ruckusmattster/xtm-led-driver/hardware/board_b/board_b-sheets.md

# Board B (controller): sheet tables

Generated by `design/build.py` from `design/board_b.py`. Every pin of every part is listed; `NC` means deliberately unconnected. Net names in CAPS match the KiCad netlist.

## Sheet B1: Power

| Ref | Value | Part | Footprint | Pins (pin name: net) |
| --- | --- | --- | --- | --- |
| C1 | 10uF | CL21A106KAYNNNE | `Capacitor_SMD:C_0805_2012Metric` | 1: +5V_SYS; 2: GND |
| D1 | B5819W | B5819W SL | `Diode_SMD:D_SOD-123` | 1 K: +5V_SYS; 2 A: +5V5_F |
| FB1 | 600R@100MHz 2A | UPZ2012E601-2R0TF | `Inductor_SMD:L_0805_2012Metric` | 1: +5V5_IN; 2: +5V5_F |
| J1 | 2x5 box header |  | `Connector_IDC:IDC-Header_2x05_P2.54mm_Vertical` | 1: +5V5_IN; 2: GND; 3: +5V5_IN; 4: GND; 5: TXD_A; 6: GND; 7: RXD_A; 8: BOOT0_A; 9: A_OK; 10: NRST_A |

Notes:

- **J1**: Same pinout as Board A's J3; a straight-through ribbon
- **D1**: Keeps the module's USB 5 V (its 5V pin) out of Board A when it's powered from USB
- **C1**: At U1's 5V pin

## Sheet B2: ESP32-S3-Zero

| Ref | Value | Part | Footprint | Pins (pin name: net) |
| --- | --- | --- | --- | --- |
| C3 | 100nF | CC0603KRX7R9BB104 | `Capacitor_SMD:C_0603_1608Metric` | 1: +3V3; 2: GND |
| U1 | ESP32-S3-Zero-M | ESP32-S3-Zero-M | `XTM:ESP32-S3-Zero_Socket` | 1 5V: +5V_SYS; 2 GND: GND; 3 3V3: +3V3; 4 GP1: LINK_TX; 5 GP2: LINK_RX; 6 GP3: SPARE_IO3; 7 GP4: ENC_A; 8 GP5: ENC_B; 9 GP6: ENC_SW; 10 GP7: SYNC; 11 GP8: BOOT0_OUT; 12 GP9: A_OK_IN; 13 GP10: NRST_OUT; 14 GP11: LED_R; 15 GP12: LED_G; 16 GP13: LED_B; 17 RX/GP44: SPARE_IO44; 18 TX/GP43: SPARE_IO43 |

Notes:

- **U1**: Plugged into two 1x9 sockets on the bottom side, component side away from the board, antenna end at the board edge. IO4-IO13 keep the WROOM design's assignments; the link moves to IO1/IO2 so UART0 (IO43/IO44, which the boot ROM talks on) stays off Board A's line. IO3 is a strapping pin: left as a spare
- **C3**: At U1's 3V3 pin

## Sheet B3: Controls, indicators and link

| Ref | Value | Part | Footprint | Pins (pin name: net) |
| --- | --- | --- | --- | --- |
| C8 | 10nF |  | `Capacitor_SMD:C_0603_1608Metric` | 1: ENC_A; 2: GND |
| C9 | 10nF |  | `Capacitor_SMD:C_0603_1608Metric` | 1: ENC_B; 2: GND |
| C10 | 10nF |  | `Capacitor_SMD:C_0603_1608Metric` | 1: ENC_SW; 2: GND |
| C11 | 10nF |  | `Capacitor_SMD:C_0603_1608Metric` | 1: SYNC; 2: GND |
| D3 | red | KT-0603R | `LED_SMD:LED_0603_1608Metric` | 1 K: LED_R; 2 A: LED_R_A |
| D4 | green | KT-0603G | `LED_SMD:LED_0603_1608Metric` | 1 K: LED_G; 2 A: LED_G_A |
| D5 | blue | KT-0603B | `LED_SMD:LED_0603_1608Metric` | 1 K: LED_B; 2 A: LED_B_A |
| FID1 | FID |  | `Fiducial:Fiducial_1mm_Mask2mm` |  |
| FID2 | FID |  | `Fiducial:Fiducial_1mm_Mask2mm` |  |
| FID3 | FID |  | `Fiducial:Fiducial_1mm_Mask2mm` |  |
| H1 | M3 |  | `MountingHole:MountingHole_3.2mm_M3` |  |
| H2 | M3 |  | `MountingHole:MountingHole_3.2mm_M3` |  |
| J3 | JST PH 2 | B2B-PH-K-S(LF)(SN) | `Connector_JST:JST_PH_B2B-PH-K_1x02_P2.00mm_Vertical` | 1: SYNC_RAW; 2: GND |
| J4 | 1x5 header |  | `Connector_PinHeader_2.54mm:PinHeader_1x05_P2.54mm_Vertical` | 1: +3V3; 2: SPARE_IO3; 3: SPARE_IO43; 4: SPARE_IO44; 5: GND |
| R7 | 10k | 0603WAF1002T5E | `Resistor_SMD:R_0603_1608Metric` | 1: +3V3; 2: ENC_A_RAW |
| R8 | 10k | 0603WAF1002T5E | `Resistor_SMD:R_0603_1608Metric` | 1: ENC_A_RAW; 2: ENC_A |
| R9 | 10k | 0603WAF1002T5E | `Resistor_SMD:R_0603_1608Metric` | 1: +3V3; 2: ENC_B_RAW |
| R10 | 10k | 0603WAF1002T5E | `Resistor_SMD:R_0603_1608Metric` | 1: ENC_B_RAW; 2: ENC_B |
| R11 | 10k | 0603WAF1002T5E | `Resistor_SMD:R_0603_1608Metric` | 1: +3V3; 2: ENC_SW_RAW |
| R12 | 10k | 0603WAF1002T5E | `Resistor_SMD:R_0603_1608Metric` | 1: ENC_SW_RAW; 2: ENC_SW |
| R13 | 10k | 0603WAF1002T5E | `Resistor_SMD:R_0603_1608Metric` | 1: +3V3; 2: SYNC_RAW |
| R14 | 10k | 0603WAF1002T5E | `Resistor_SMD:R_0603_1608Metric` | 1: SYNC_RAW; 2: SYNC |
| R15 | 1k | 0603WAF1001T5E | `Resistor_SMD:R_0603_1608Metric` | 1: +3V3; 2: LED_R_A |
| R16 | 220R | 0603WAF2200T5E | `Resistor_SMD:R_0603_1608Metric` | 1: +3V3; 2: LED_G_A |
| R17 | 220R | 0603WAF2200T5E | `Resistor_SMD:R_0603_1608Metric` | 1: +3V3; 2: LED_B_A |
| R18 | 100R | 0603WAF1000T5E | `Resistor_SMD:R_0603_1608Metric` | 1: LINK_TX; 2: RXD_A |
| R19 | 100R | 0603WAF1000T5E | `Resistor_SMD:R_0603_1608Metric` | 1: TXD_A; 2: LINK_RX |
| R20 | 100R | 0603WAF1000T5E | `Resistor_SMD:R_0603_1608Metric` | 1: BOOT0_OUT; 2: BOOT0_A |
| R21 | 100R | 0603WAF1000T5E | `Resistor_SMD:R_0603_1608Metric` | 1: A_OK; 2: A_OK_IN |
| R22 | 100k | 0603WAF1003T5E | `Resistor_SMD:R_0603_1608Metric` | 1: A_OK_IN; 2: GND |
| R23 | 100R | 0603WAF1000T5E | `Resistor_SMD:R_0603_1608Metric` | 1: NRST_OUT; 2: NRST_A |
| SW3 | PEC11R-4220F-S0024 | PEC11R-4220F-S0024 | `Rotary_Encoder:RotaryEncoder_Alps_EC11E-Switch_Vertical_H20mm_CircularMountingHoles` | A A: ENC_A_RAW; B B: ENC_B_RAW; C C: GND; S1 S1: ENC_SW_RAW; S2 S2: GND; MP MP: GND |
| SW4 | SYNC |  | `Button_Switch_SMD:SW_SPST_B3S-1000` | 1: SYNC_RAW; 2: GND |
| TP1 | TP |  | `TestPoint:TestPoint_Pad_D1.0mm` | 1: +5V_SYS |
| TP2 | TP |  | `TestPoint:TestPoint_Pad_D1.0mm` | 1: +3V3 |
| TP3 | TP |  | `TestPoint:TestPoint_Pad_D1.0mm` | 1: GND |

Notes:

- **SW3**: Mounting lugs to GND
- **J3**: External panel sync button in parallel with SW4
- **R22**: Unplugged ribbon reads as 'Board A not OK'
- **R23**: IO10 is driven open-drain by firmware
- **J4**: Optional spare header: IO43/IO44 are UART0 (the ESP32's console), IO3 a strapping pin

## Net list

| Net | Connections |
| --- | --- |
| +3V3 | C3.1, J4.1, R7.1, R9.1, R11.1, R13.1, R15.1, R16.1, R17.1, TP2.1, U1.3 |
| +5V5_F | D1.2, FB1.2 |
| +5V5_IN | FB1.1, J1.1, J1.3 |
| +5V_SYS | C1.1, D1.1, TP1.1, U1.1 |
| A_OK | J1.9, R21.1 |
| A_OK_IN | R21.2, R22.1, U1.12 |
| BOOT0_A | J1.8, R20.2 |
| BOOT0_OUT | R20.1, U1.11 |
| ENC_A | C8.1, R8.2, U1.7 |
| ENC_A_RAW | R7.2, R8.1, SW3.A |
| ENC_B | C9.1, R10.2, U1.8 |
| ENC_B_RAW | R9.2, R10.1, SW3.B |
| ENC_SW | C10.1, R12.2, U1.9 |
| ENC_SW_RAW | R11.2, R12.1, SW3.S1 |
| GND | C1.2, C3.2, C8.2, C9.2, C10.2, C11.2, J1.2, J1.4, J1.6, J3.2, J4.5, R22.2, SW3.C, SW3.MP, SW3.S2, SW4.2, TP3.1, U1.2 |
| LED_B | D5.1, U1.16 |
| LED_B_A | D5.2, R17.2 |
| LED_G | D4.1, U1.15 |
| LED_G_A | D4.2, R16.2 |
| LED_R | D3.1, U1.14 |
| LED_R_A | D3.2, R15.2 |
| LINK_RX | R19.2, U1.5 |
| LINK_TX | R18.1, U1.4 |
| NRST_A | J1.10, R23.2 |
| NRST_OUT | R23.1, U1.13 |
| RXD_A | J1.7, R18.2 |
| SPARE_IO3 | J4.2, U1.6 |
| SPARE_IO43 | J4.3, U1.18 |
| SPARE_IO44 | J4.4, U1.17 |
| SYNC | C11.1, R14.2, U1.10 |
| SYNC_RAW | J3.1, R13.2, R14.1, SW4.1 |
| TXD_A | J1.5, R19.1 |
