ruckusmattster/xtm-led-driver/docs/images/board-a-iso.png

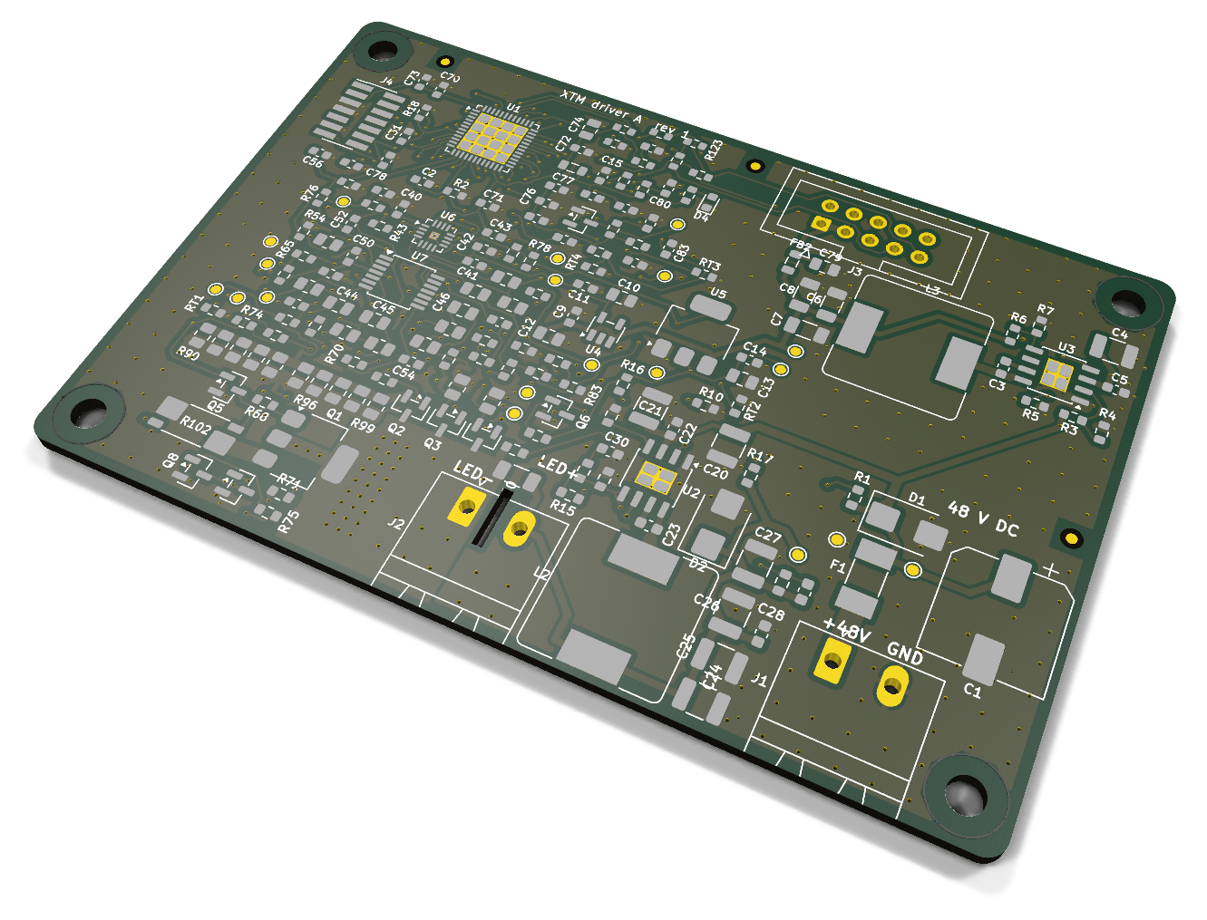
docs/images/board-a-iso.png
