ruckusmattster/xtm-led-driver/layout/out/board_a/board_a-1-FCu_FSilkS.png

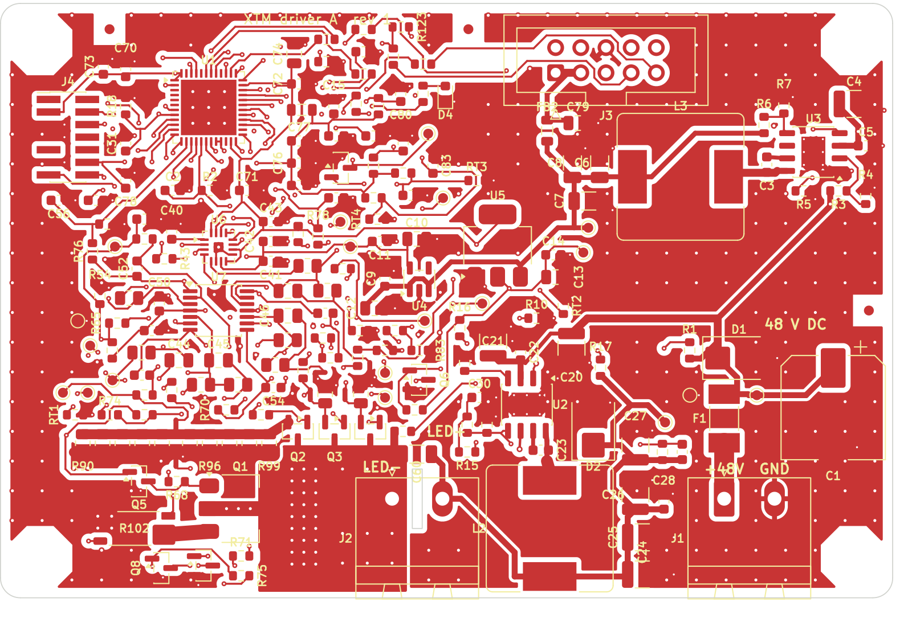
layout/out/board_a/board_a-1-FCu_FSilkS.png
