ruckusmattster/xtm-led-driver/layout/out/board_a/board_a-2-BCu_EdgeCuts.png

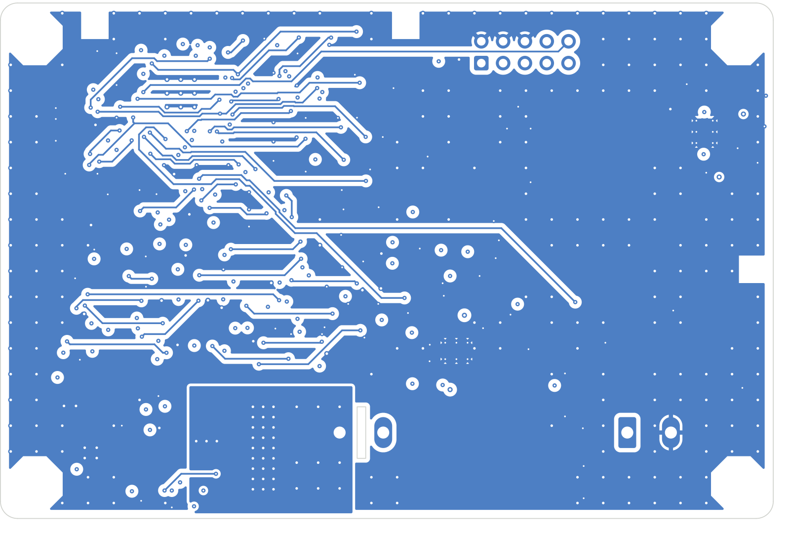
layout/out/board_a/board_a-2-BCu_EdgeCuts.png
