ruckusmattster/xtm-led-driver/layout/out/board_a/board_a-3-In2Cu_EdgeCuts.png

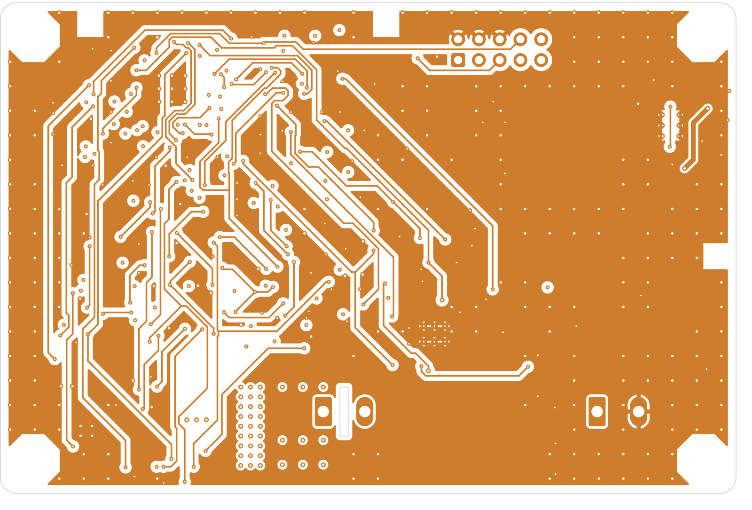
layout/out/board_a/board_a-3-In2Cu_EdgeCuts.png
