ruckusmattster/xtm-led-driver/layout/out/board_b/board_b-1-FCu_FSilkS.png

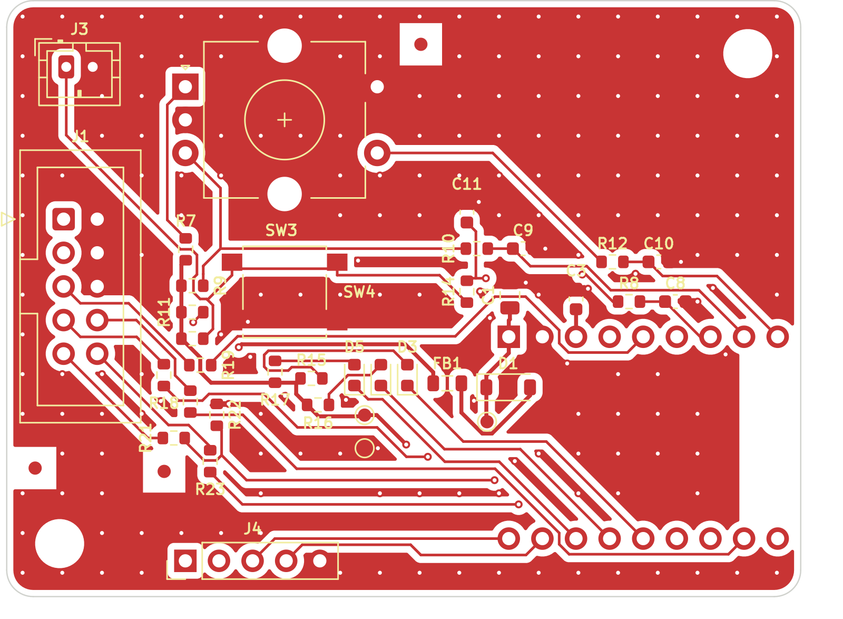
layout/out/board_b/board_b-1-FCu_FSilkS.png
