ruckusmattster/xtm-led-driver/layout/out/board_b/board_b-2-BCu_BSilkS.png

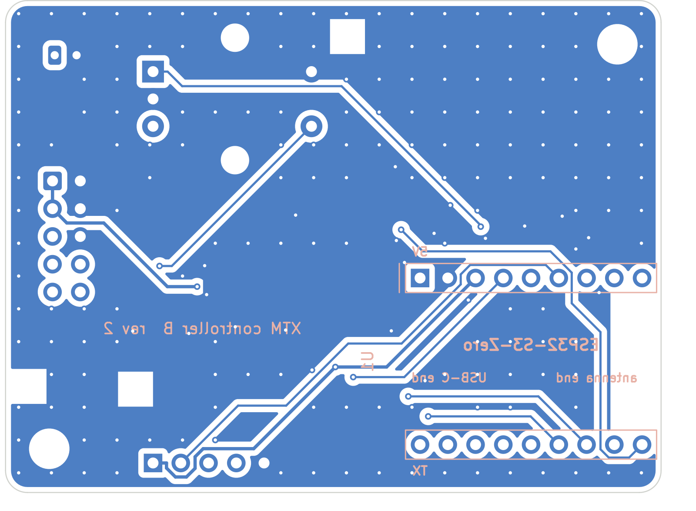
layout/out/board_b/board_b-2-BCu_BSilkS.png
